klehnst/ESP32-Adrafruit-BNO085-HomeAssistant-Caravan-Levelsensor-MQTT/sensor.h

#ifndef SENSOR_H
#define SENSOR_H

#include <Arduino.h>
#include "config.h"

bool sensorInit();
void sensorLoop();
void sensorSetTare();
void sensorAdjustTare(float deltaPitch, float deltaRoll);
void sensorResetTare();
void sensorResetCalibration();
float getPitchDeg();
float getRollDeg();
String getCalStatusString();

#endif // SENSOR_H
