klehnst/ESP32-Adrafruit-BNO085-HomeAssistant-Caravan-Levelsensor-MQTT/mqtt_ha.h

#ifndef MQTT_HA_H
#define MQTT_HA_H

#include <Arduino.h>
#include "config.h"

void mqttInit();
void mqttLoop();
bool mqttIsConnected();
void mqttPublishDiscovery();
void mqttPublishState();

#endif // MQTT_HA_H
